koppanyh/ProjectARECS/seniorproject/text/pictures/20180110_102803.jpg

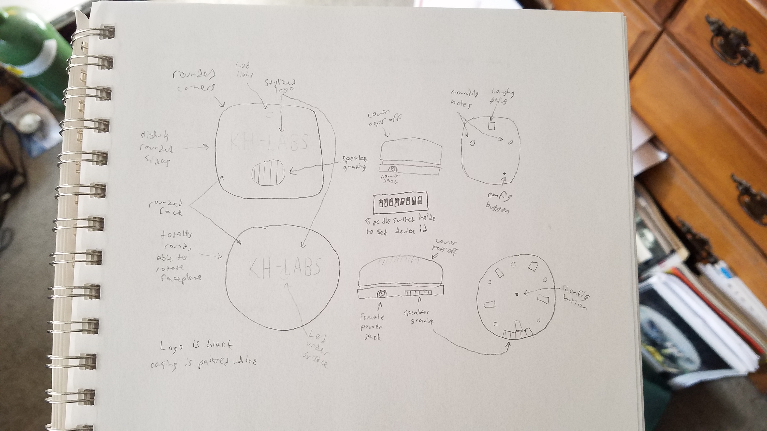
seniorproject/text/pictures/20180110_102803.jpg
