koppanyh/ProjectARECS/seniorproject/text/pictures/20180110_102817.jpg

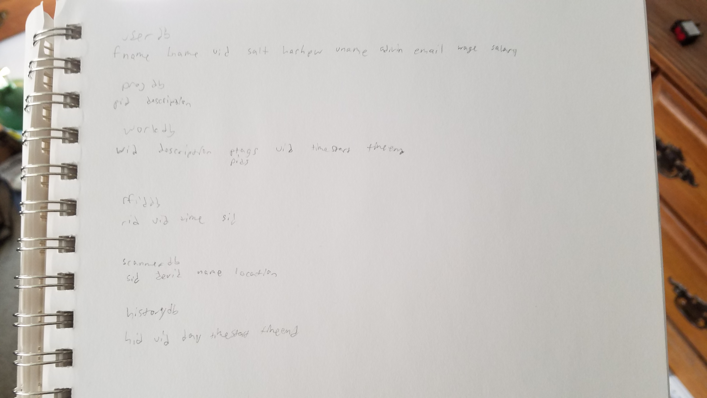
seniorproject/text/pictures/20180110_102817.jpg
