koppanyh/ProjectARECS/seniorproject/text/pictures/20180305_090607.jpg

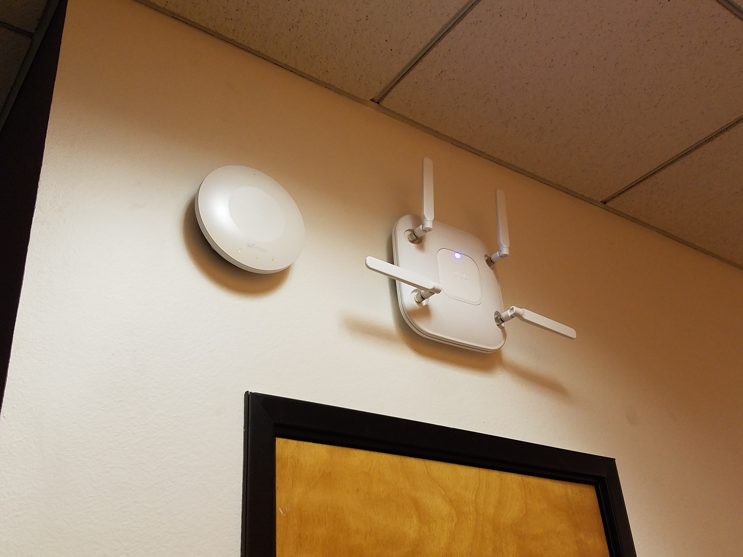
seniorproject/text/pictures/20180305_090607.jpg
