koppanyh/ProjectARECS/seniorproject/text/pictures/20180330_172824.jpg

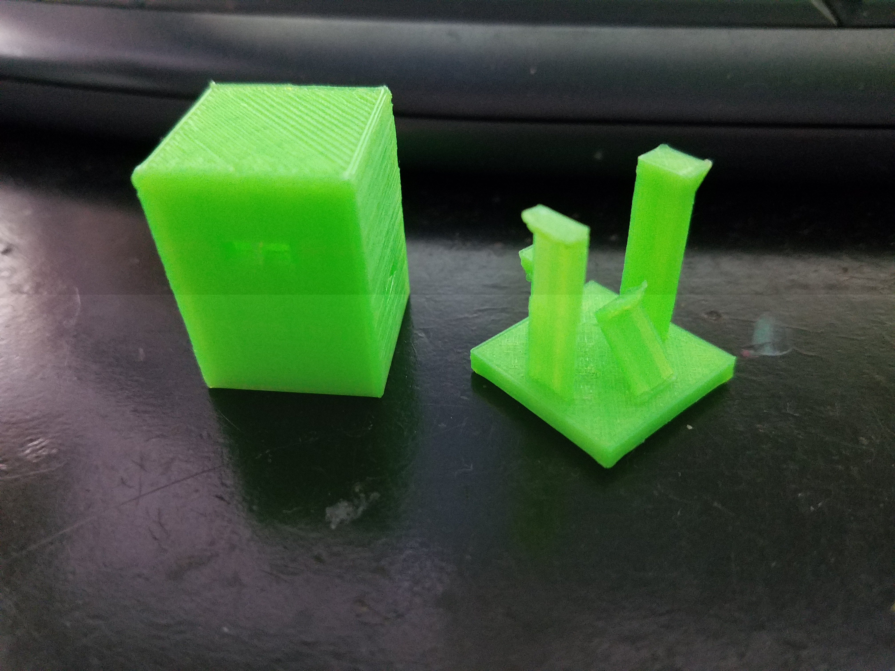
seniorproject/text/pictures/20180330_172824.jpg
