koppanyh/ProjectARECS/seniorproject/text/pictures/20180331_153744.jpg

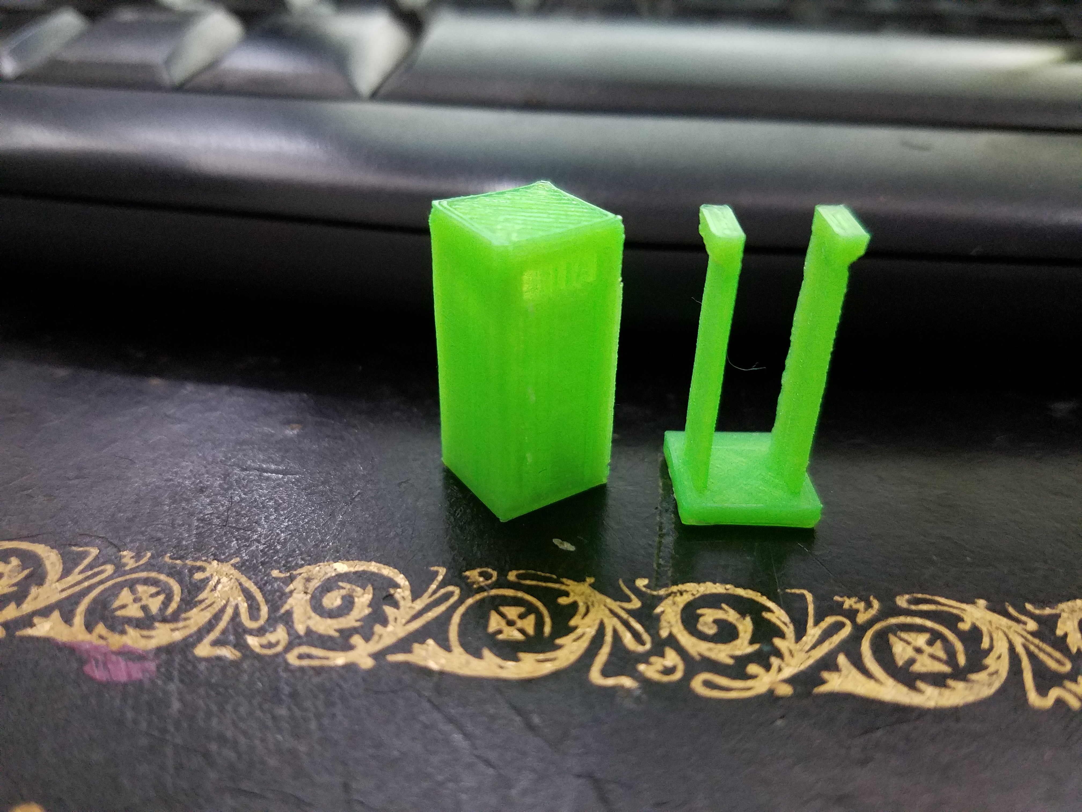
seniorproject/text/pictures/20180331_153744.jpg
