koppanyh/ProjectARECS/seniorproject/text/pictures/20180331_222629.jpg

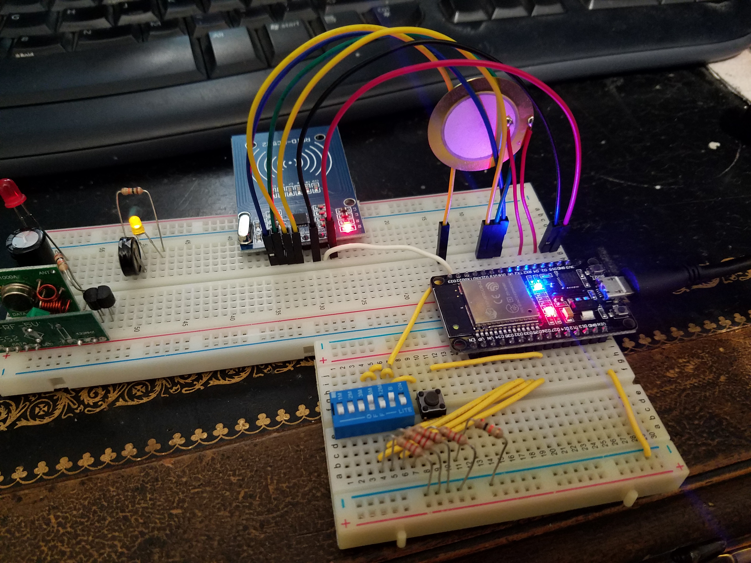
seniorproject/text/pictures/20180331_222629.jpg
