koppanyh/ProjectARECS/seniorproject/text/pictures/20180408_182519.jpg

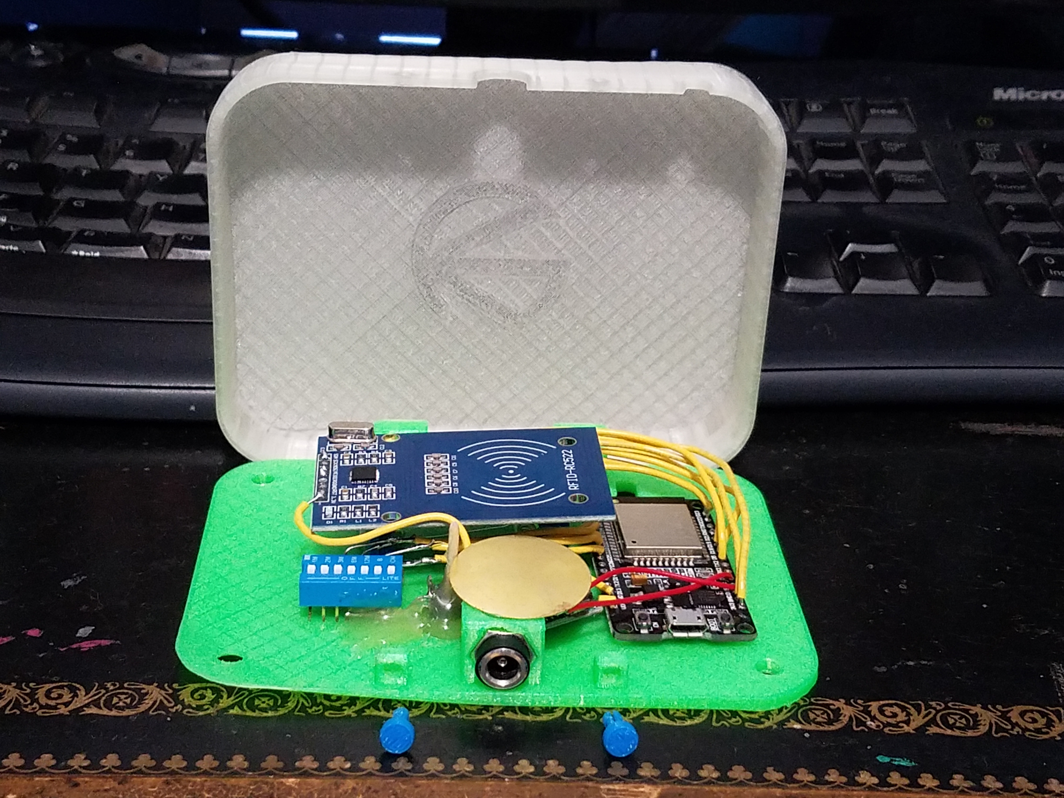
seniorproject/text/pictures/20180408_182519.jpg
