koppanyh/ProjectARECS/seniorproject/text/pictures/20180408_182607.jpg

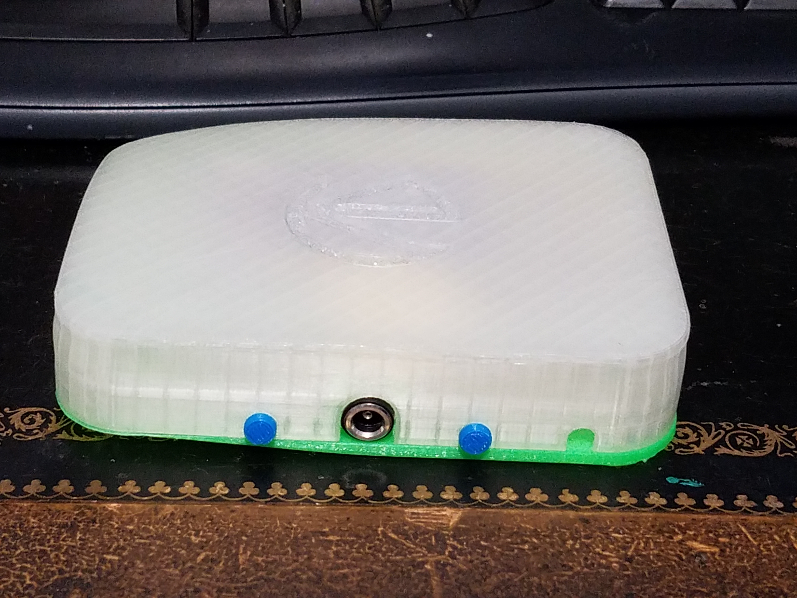
seniorproject/text/pictures/20180408_182607.jpg
