koppanyh/ProjectARECS/seniorproject/text/pictures/20180408_182653.jpg

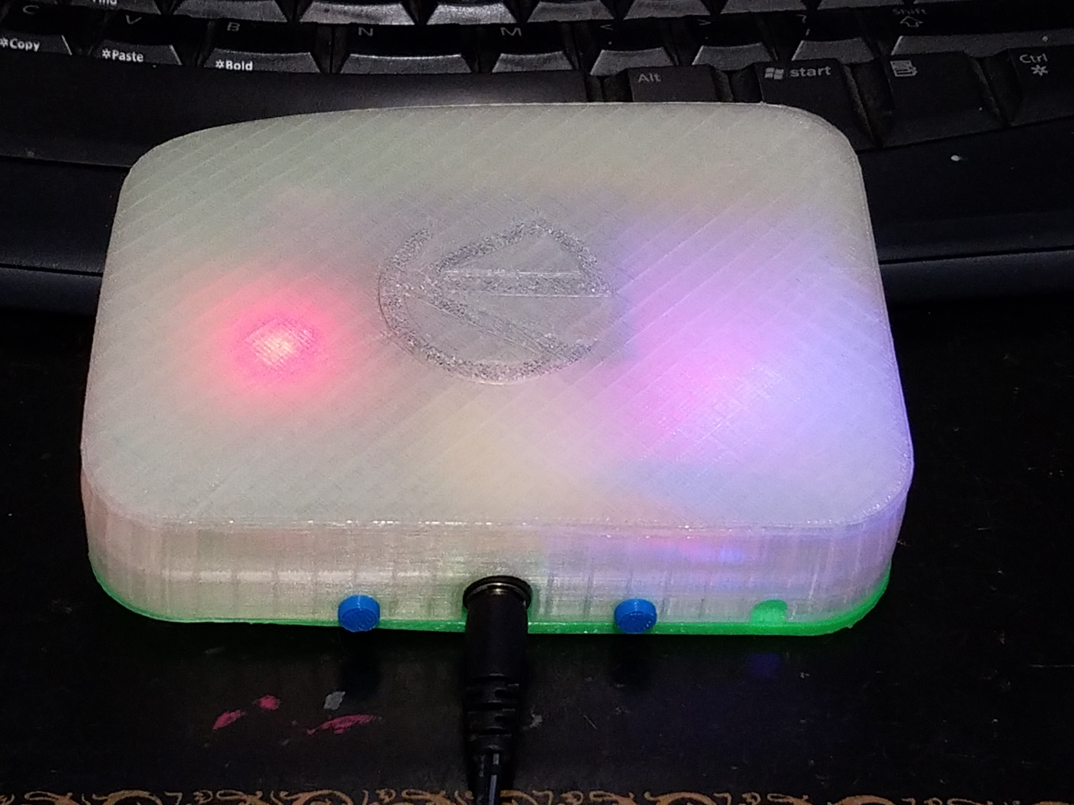
seniorproject/text/pictures/20180408_182653.jpg
