koppanyh/ProjectARECS/seniorproject/text/pictures/20180408_184723.jpg

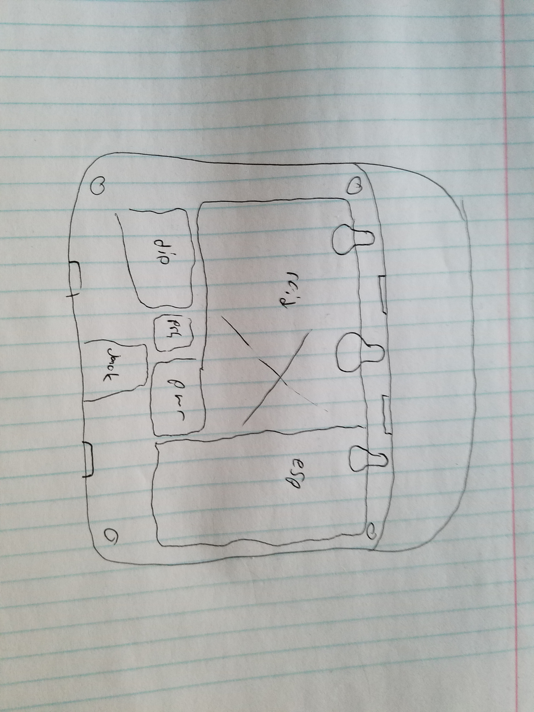
seniorproject/text/pictures/20180408_184723.jpg
