koppanyh/ProjectARECS/seniorproject/text/pictures/20180430_155907.jpg

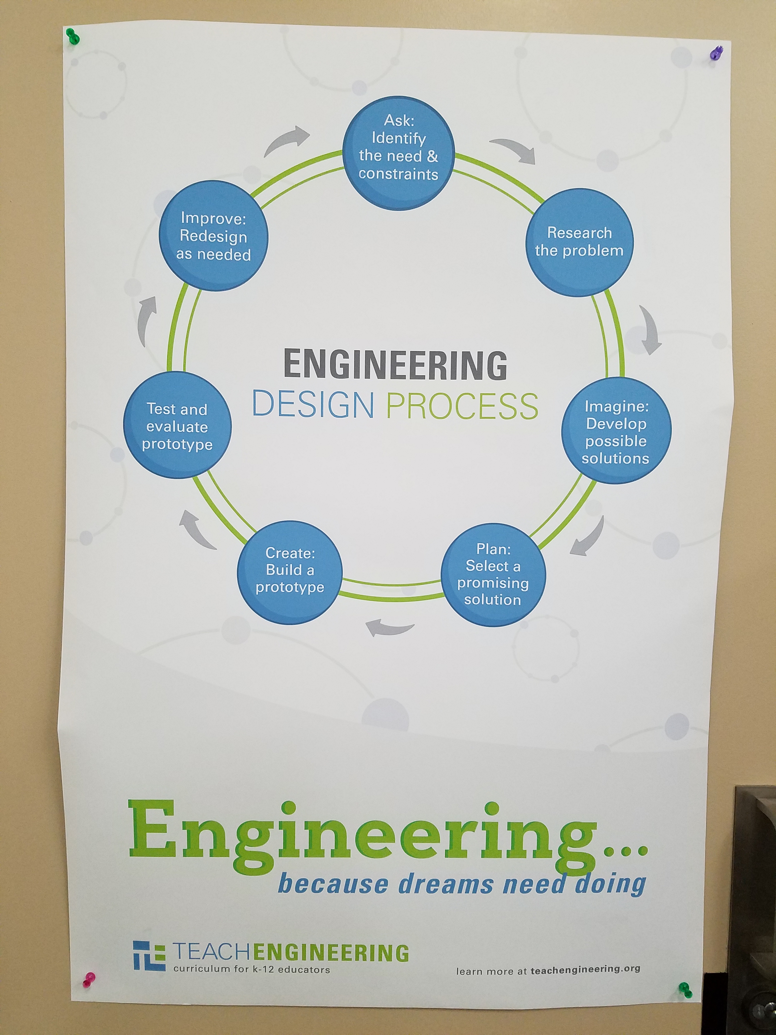
seniorproject/text/pictures/20180430_155907.jpg
