koppanyh/ProjectARECS/seniorproject/text/pictures/20180513_190717.jpg

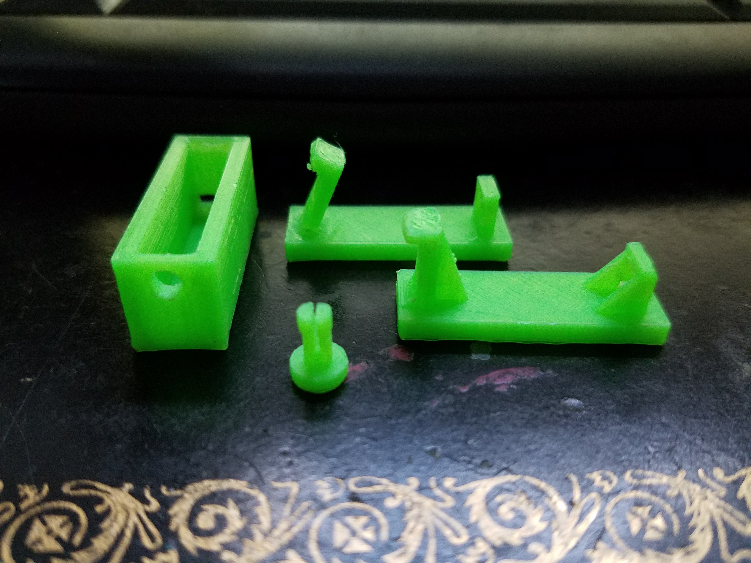
seniorproject/text/pictures/20180513_190717.jpg
