koppanyh/ProjectARECS/seniorproject/text/pictures/20180513_190753.jpg

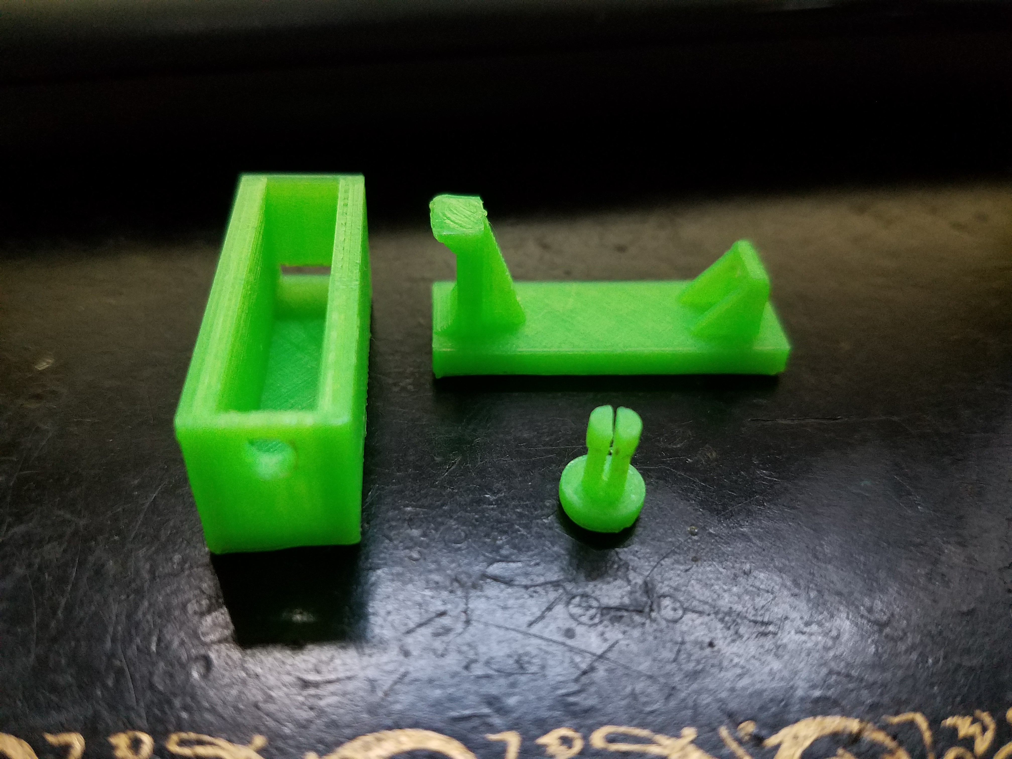
seniorproject/text/pictures/20180513_190753.jpg
