koppanyh/ProjectARECS/seniorproject/text/pictures/20180513_190812.jpg

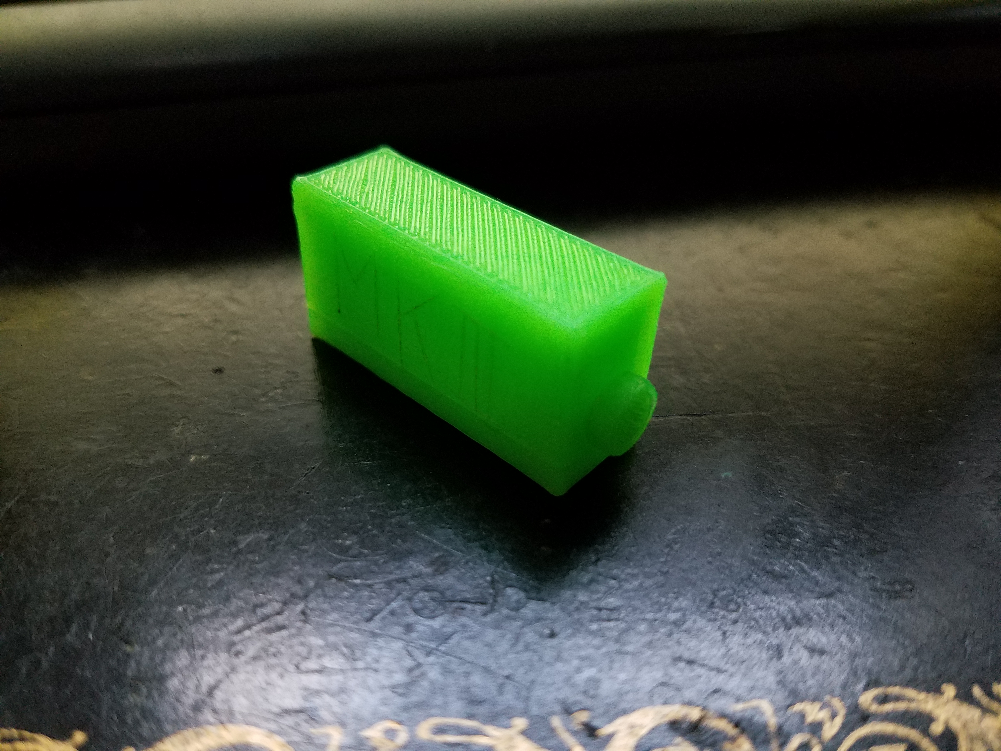
seniorproject/text/pictures/20180513_190812.jpg
