koppanyh/ProjectARECS/seniorproject/text/pictures/blockdiagram.png

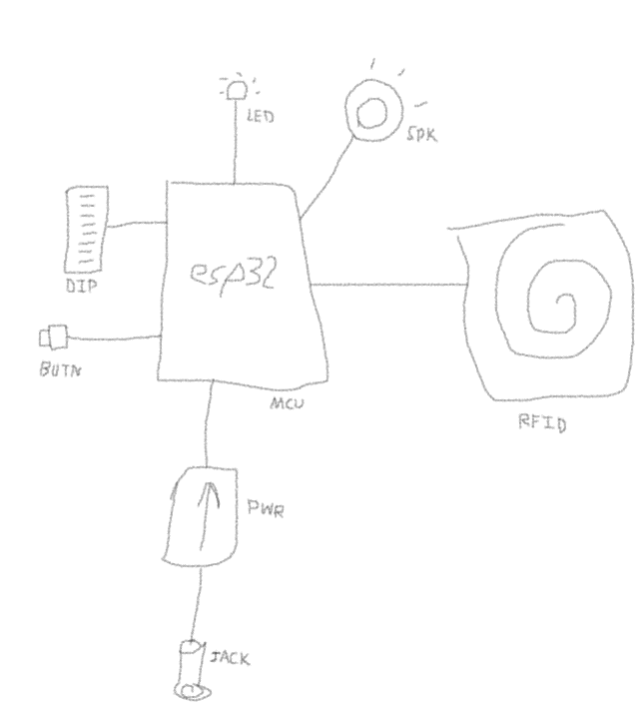
seniorproject/text/pictures/blockdiagram.png
