koppanyh/ProjectARECS/seniorproject/text/pictures/Screenshot_20180318-220846.png

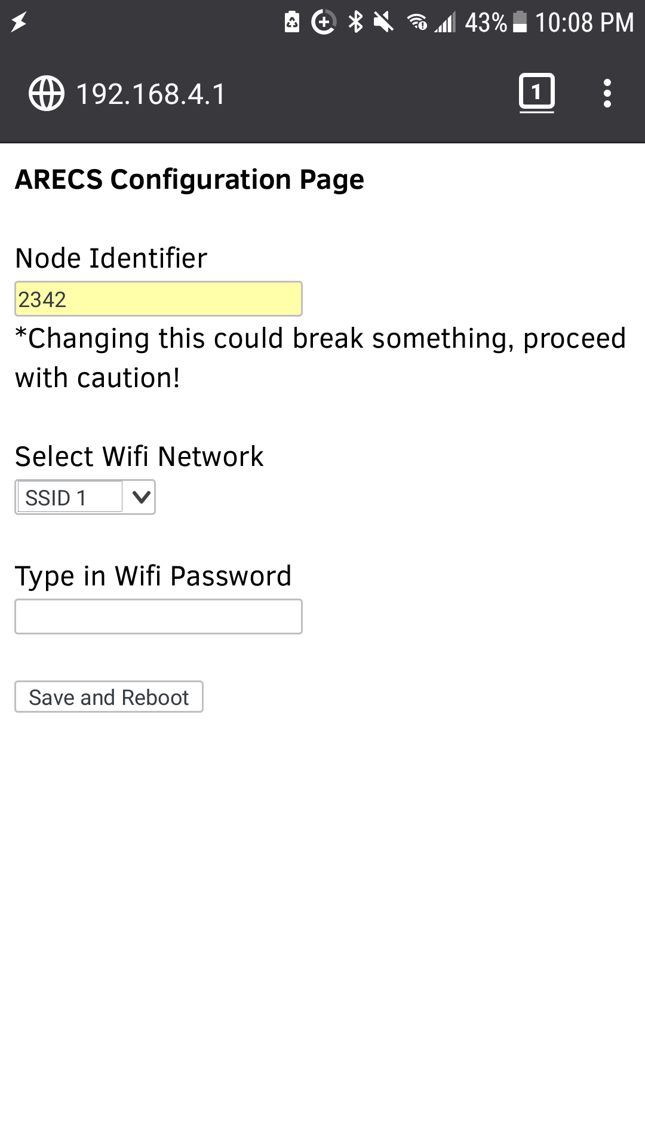
seniorproject/text/pictures/Screenshot_20180318-220846.png
