koppanyh/ProjectARECS/untitled.png

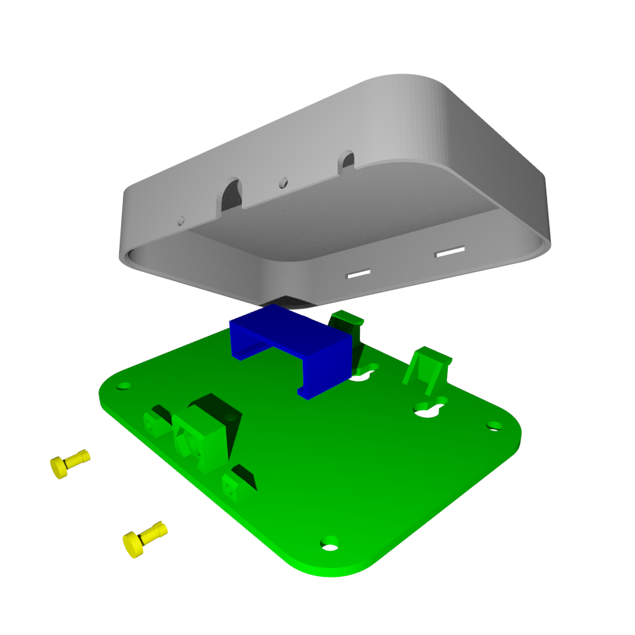
untitled.png
