koppanyh/ProjectARECS/seniorproject/tests/snaplid2.fcstd

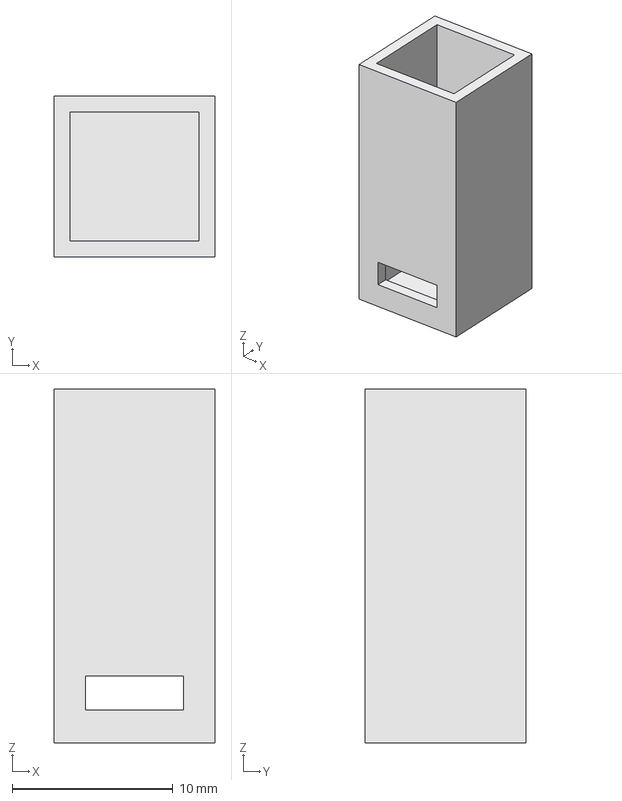
[picture p60: CAD file, 2018-04-01]
seniorproject/tests/snaplid2.fcstd
10.0 x 10.0 x 22.0 mm
