koppanyh/ProjectARECS/seniorproject/tests/snap2.fcstd

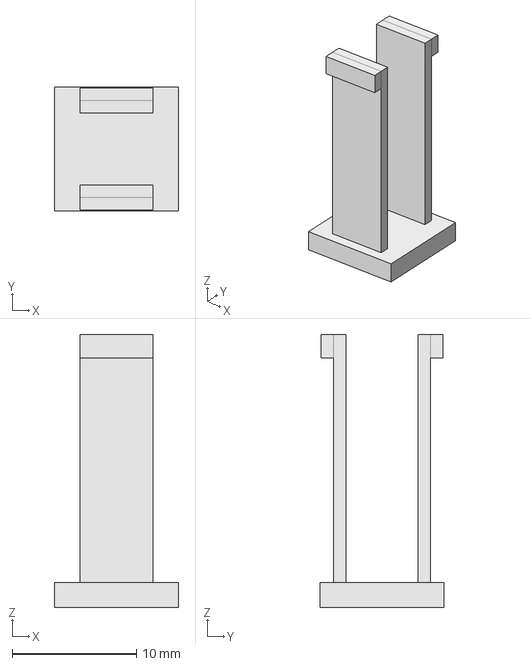
[picture p61: CAD file, 2018-04-01]
seniorproject/tests/snap2.fcstd
10.0 x 10.0 x 22.0 mm
