koppanyh/ProjectARECS/seniorproject/tests/snaplid.fcstd

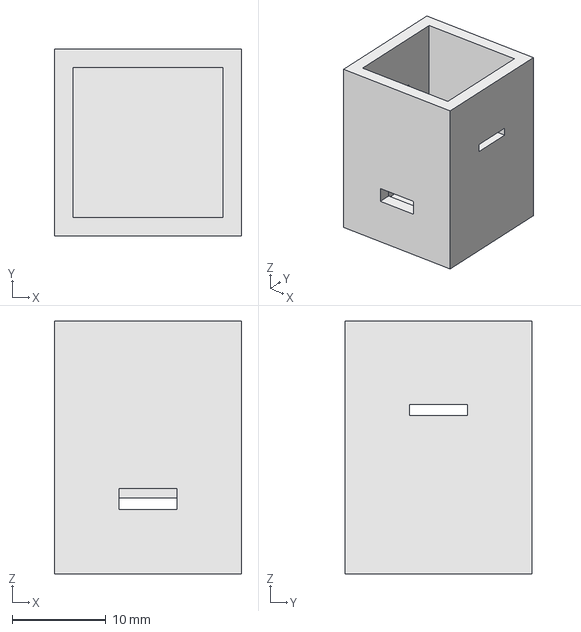
[picture p62: CAD file, 2018-04-01]
seniorproject/tests/snaplid.fcstd
20.0 x 20.0 x 27.0 mm
